mikesmitty/power-manifold/docs/src/content/docs/index.mdx

---
title: Power Manifold
description: A six-port USB-C power supply for single-board computers and other USB-C devices, with per-port control, priority-based power sharing and Home Assistant support.
template: splash
hero:
  image:
    # A plain img: Starlight would crop an image file to a square.
    html: 'Power Manifold chassis from the front right, showing the Ethernet jack, six numbered USB-C ports, the exhaust fan and the XT60 power input.'
  tagline: Six USB-C ports up to 100 W each, from one 24 V supply. Switch, name, limit and monitor every port from a browser or Home Assistant.
  actions:
    - text: Get started
      link: /setup/first-time-setup/
      icon: right-arrow
    - text: Source on GitHub
      link: https://github.com/mikesmitty/power-manifold
      icon: external
      variant: minimal
---

import { CardGrid, LinkCard } from '@astrojs/starlight/components';
import AdapterClutter from '../../components/AdapterClutter.astro';

<CardGrid>
	<LinkCard
		title="Set up your ports"
		description="Names, on/off at power-up, voltage and current limits, auto-off when charged."
		href="/guide/port-settings/"
	/>
	<LinkCard
		title="Share power between ports"
		description="Set the power budget and port priorities for a supply smaller than 600 W."
		href="/guide/sharing-power/"
	/>
	<LinkCard
		title="Add it to Home Assistant"
		description="Connect it to your MQTT broker and every port appears automatically."
		href="/guide/home-assistant/"
	/>
	<LinkCard
		title="Read the lights"
		description="What each port light and the chassis light mean, and what the button does."
		href="/guide/front-panel/"
	/>
	<LinkCard
		title="Troubleshooting"
		description="What a red light or a problem warning means, and what to do about it."
		href="/guide/troubleshooting/"
	/>
	<LinkCard
		title="Hardware and firmware"
		description="Architecture, building the firmware and the serial console, for developers."
		href="/developers/architecture/"
	/>
</CardGrid>

## What it does

<AdapterClutter />

<div class="features">
	<div class="feature">
		<h3>Six ports, up to 100 W each</h3>
		<p>Powers Raspberry Pis, phones, mini PCs and laptops at 5, 9, 12, 15 or 20 V, or PPS, with up to 5 A on a 5 A cable.</p>
	</div>
	<div class="feature">
		<h3>Shares power by priority</h3>
		<p>Set the size of your power supply and a priority for each port. When devices ask for more than the supply can give, the least important ports are turned down. Nothing is switched off.</p>
	</div>
	<div class="feature">
		<h3>Works with Home Assistant</h3>
		<p>Every port shows up with its power, an on/off switch and its settings, ready for dashboards, the energy panel and automations.</p>
	</div>
	<div class="feature">
		<h3>Status lights and live readings</h3>
		<p>A light above each port shows what it is doing, and the built-in web interface shows live power for every port.</p>
	</div>
</div>
