mikesmitty/power-manifold/docs/src/content/docs/integrations/ups.mdx

---
title: UPS power supply
description: Unofficial support for running Power Manifold from a Mean Well LAD-xxxBU battery-backed supply and seeing AC power and battery status in Home Assistant.
sidebar:
  order: 5
  badge:
    text: Unofficial
    variant: caution
---

import { Aside } from '@astrojs/starlight/components';
import Flow from '../../../components/Flow.astro';

<Aside type="caution" title="Unofficial">
UPS monitoring is not an officially supported configuration. The enclosure
provides no external access to the controller's UPS header, so connecting
the supply's serial lead requires opening the chassis. Support has been
verified only against a simulated supply.
</Aside>

Power Manifold can run from a Mean Well **LAD-xxxBU** security power supply,
which charges a battery and switches to it when AC power fails. Use a model
whose name ends in **BU**:

- **B** models charge a 24 V battery and have a 27.6 V output. The **A**
  models (13.8 V) and **C** models (about 41 V) don't suit Power
  Manifold's 24 V input.
- **U** models have the serial port Power Manifold needs.

## Connecting it

<Flow
	nodes={[
		{ title: 'AC power' },
		{ title: 'Mean Well LAD-xxxBU', detail: 'Runs from its battery when AC power fails' },
		{ title: 'Power Manifold', detail: 'Shows AC power and battery', highlight: true },
	]}
	links={[{ label: 'AC' }, { label: ['27.6 V to the XT60', 'CN2 to the UPS header'] }]}
/>

Connect the supply's output to the chassis XT60 input as usual. Then
connect the supply's serial port (on its CN2 header) to the controller
card's 3-pin **UPS** header. The controller finds the supply by itself
within a few seconds.

## What you get

Once the supply answers, the controller shows:

- whether AC power is on, whether it's running on battery and whether
  the battery is charging;
- battery voltage, AC voltage and load current.

These appear in the web interface's chassis line, in Home Assistant as *UPS AC
input*, *UPS on battery* and *UPS charging* plus three sensors, in the
[MQTT status](/integrations/mqtt/) and in the
[status JSON](/integrations/http-api/).

Running on battery, or a battery problem such as a missing, reversed or
failing battery, raises the **Problem** warning. You can use it to shut
down your Raspberry Pis gracefully before the battery runs out.

The UPS entities appear only once a supply answers. A chassis without one
shows none.
