mikesmitty/power-manifold/firmware/controller/src/engine/engine.c

#include "engine.h"
#include "i2c_diag.h"

#include <string.h>

#include "hardware/gpio.h"
#include "hardware/i2c.h"
#include "pico/flash.h"
#include "pico/stdlib.h"

#include "budget.h"
#include "fan_policy.h"
#include "flash_map.h"
#include "ipc.h"
#include "leds.h"
#include "manifold.h"
#include "pins.h"
#include "port_fsm.h"
#include "settings.h"
#include "stack_probe.h"
#include "tca9539.h"
#include "tca9548a.h"

#ifdef PWRMAN_FAKE_BLADES
#include "sim/sim_blades.h"
#include "sim/sim_inject.h"
#include "sim/sim_scenario.h"
#endif

#define TICK_MS 10 // 100 Hz supervisory rate
#define PRESENCE_REFRESH_TICKS 10 // full presence re-read every 100ms

static volatile bool alert_irq;
static volatile bool exp_irq;

// Expander reads missed in a row (one try per 100 ms) before the mux is
// reset, and before the expander itself is
#define EXP_FAILS_MUX_RESET 5
#define EXP_FAILS_RECOVER   50

static bool present[NUM_PORTS];
static uint8_t exp_fail_streak;
static bool warm_start;   // see engine_main
static uint8_t adopted;   // ports kept powered through the start

volatile uint8_t engine_stage;
volatile uint32_t engine_stage_us;
#define STAGE(n) do { engine_stage_us = time_us_32(); engine_stage = (n); } while (0)

// Delivered energy, integrated at the tick rate in mW·ms (µJ). uint64 is
// centuries of headroom; the mWh views in telemetry wrap after ~4.9 years
// of continuous 100W, which resets HA's total_increasing meters harmlessly.
static uint64_t port_energy_uj[NUM_PORTS];
static uint64_t total_energy_uj;

#ifndef PWRMAN_FAKE_BLADES
static void gpio_irq_handler(uint gpio, uint32_t events) {
    (void)events;
    if (gpio == PIN_ALERT_N) alert_irq = true;
    else if (gpio == PIN_EXP_INT_N) exp_irq = true;
}
#endif

// GLOBAL_ALERT# level; the sim stands in for the wire-OR line in fake builds
static bool alert_line_active(void) {
#ifdef PWRMAN_FAKE_BLADES
    return sim_alert_asserted();
#else
    return !gpio_get(PIN_ALERT_N);
#endif
}

static void refresh_presence(void) {
    uint16_t inputs;
    if (!tca9539_read_inputs(&inputs)) {
        // I2C trouble at the expander is chassis-level. After a few misses
        // the mux is reset, which frees a downstream segment that hung the
        // bus and costs no port anything. The expander keeps every EN where
        // it was through all of that, so it is left alone: only when it has
        // been out of reach for seconds — nobody can switch a port off then
        // — is it reset and its EN pattern written straight back
        // (tca9539_recover). That reset floats the EN lines for the moment
        // between the pulse and the write, which a running port will
        // notice; it is the last resort, not the first.
        exp_fail_streak++;
        if (exp_fail_streak % EXP_FAILS_MUX_RESET == 0) {
            tca9548a_hw_reset();
            if (exp_fail_streak == EXP_FAILS_MUX_RESET) {
                engine_evt_t e = {.type = EVT_PROBE_FAIL, .port = CHASSIS_EVT_PORT};
                ipc_evt_push(&e);
            }
        }
        if (exp_fail_streak >= EXP_FAILS_RECOVER) {
            exp_fail_streak = 0;
            tca9539_recover();
            engine_evt_t e = {.type = EVT_PROBE_FAIL, .port = CHASSIS_EVT_PORT, .code = 5};
            ipc_evt_push(&e);
        }
        return;
    }
    exp_fail_streak = 0;
    // A blade that reads as gone costs its port its power that tick, and
    // the read has nothing guarding it against a flipped bit. One that
    // says a seated blade has left is asked again, and only what both
    // reads agree on counts (PRES# is active low: a set bit is "absent").
    for (uint8_t i = 0; i < NUM_PORTS; i++) {
        if (!present[i] || tca9539_present_from(inputs, i)) continue;
        uint16_t again;
        if (!tca9539_read_inputs(&again)) return; // the next refresh decides
        inputs &= again;
        break;
    }
    for (uint8_t i = 0; i < NUM_PORTS; i++)
        present[i] = tca9539_present_from(inputs, i);
    // An expander back at its power-on registers (a reset nobody asked for)
    // has every EN floating: put its outputs and direction back and say so.
    if (tca9539_config_lost()) {
        tca9539_recover();
        engine_evt_t e = {.type = EVT_PROBE_FAIL, .port = CHASSIS_EVT_PORT, .code = 5};
        ipc_evt_push(&e);
    }
}

static void dispatch_cmd(const engine_cmd_t *cmd, uint32_t now_ms) {
    switch ((cmd_op_t)cmd->op) {
    case CMD_SET_BUDGET:
        budget_set_total(cmd->arg);
        break;
    case CMD_SET_CEILING:
        port_fsm_set_ceiling(cmd->arg);
        break;
    case CMD_FAN:
        fan_policy_set_manual(cmd->arg != 0);
        break;
    case CMD_FAN_AUTO:
        fan_policy_set_auto();
        break;
    case CMD_LED_BRIGHTNESS:
        leds_set_brightness((uint8_t)cmd->arg);
        break;
    case CMD_LED_IDENTIFY:
        leds_identify(now_ms + cmd->arg);
        break;
    case CMD_LED_CHASSIS:
        leds_set_chassis((uint8_t)cmd->arg);
        break;
    case CMD_LED_HOLD:
        leds_set_hold((uint8_t)cmd->arg);
        break;
    case CMD_LED_ACK:
        leds_ack(now_ms + cmd->arg);
        break;
    case CMD_I2C_DIAG:
#ifndef PWRMAN_FAKE_BLADES
        i2c_diag_run(cmd->arg);
#endif
        break;
    case CMD_SIM:
#ifdef PWRMAN_FAKE_BLADES
        if (sim_inject_op(cmd->arg) == SIM_SCENARIO) sim_scenario_set_running(sim_inject_value(cmd->arg) != 0);
        else sim_inject(cmd->port, cmd->arg);
#endif
        break;
    default:
        if (cmd->port < NUM_PORTS) port_fsm_cmd(cmd->port, cmd);
        break;
    }
}

void engine_main(void) {
    stack_probe_paint();
    STAGE(ENGINE_STAGE_ENTERED);
    // allow core 0 to write flash (settings) while this core is parked
    flash_safe_execute_core_init();

#ifndef PWRMAN_FAKE_BLADES
    i2c_init(I2C_BUS, I2C_BAUD);
    gpio_set_function(PIN_I2C_SDA, GPIO_FUNC_I2C);
    gpio_set_function(PIN_I2C_SCL, GPIO_FUNC_I2C);
    gpio_init(PIN_ALERT_N);
    gpio_set_dir(PIN_ALERT_N, GPIO_IN);
    // SDA/SCL and ALERT# have 4.7k external pull-ups on the controller card
    // (or wired on the pcie-breakout for a Pico 2 W). Every RP2350 pad boots
    // with its pull-down enabled and gpio_set_function/gpio_init leave it so;
    // that pull-down would sit across the external pull-up, eating noise
    // margin on every high level. Clear it.
#ifdef PWRMAN_INTERNAL_PULLUPS
    // Bench build without the three resistors: the pad pull-ups carry the
    // upstream bus (mux control, expander) at the 100 kHz in pins.h. Once a
    // mux channel is open that segment's 4.7k-to-5V pull-ups pass through
    // the switch and stiffen the upstream side as well.
    gpio_pull_up(PIN_I2C_SDA);
    gpio_pull_up(PIN_I2C_SCL);
    gpio_pull_up(PIN_ALERT_N);
#else
    gpio_disable_pulls(PIN_I2C_SDA);
    gpio_disable_pulls(PIN_I2C_SCL);
    gpio_disable_pulls(PIN_ALERT_N);
#endif
    // EXP_INT# is open-drain from the TCA9539 with no pull-up anywhere else;
    // without this the pad default (pull-down) reads it as permanently asserted.
    gpio_init(PIN_EXP_INT_N);
    gpio_set_dir(PIN_EXP_INT_N, GPIO_IN);
    gpio_pull_up(PIN_EXP_INT_N);
#else
    sim_reset();
#endif
    STAGE(ENGINE_STAGE_BUS_INIT);

    tca9548a_init();
    // A reboot with the backplane's 5 V up (firmware update, watchdog, a
    // console reboot) leaves the expander programmed and every EN where it
    // was — the reset lines are never asserted by a controller reset. Adopt
    // that state (warm start) rather than resetting it, so a reboot never
    // cuts port power; port_fsm_boot_inventory then takes the powered blades
    // under supervision without touching EN. Only an expander holding its
    // power-on state (cold start) is reset and configured from scratch,
    // outputs low FIRST, then direction (spec §6.4). While the controller
    // was down nothing arbitrated the budget or reacted to faults beyond
    // the blades' own limits; warm_probe reads what latched meanwhile.
    //
    // Which of the two it is rests on one register read, and reading it
    // wrong as cold takes every port down. So an expander that does not
    // answer is asked again for half a second, with the mux reset in between
    // (a downstream segment holding the bus is the likely cause), before
    // its silence is taken for a cold start; one that answers with anything
    // but our configuration is a cold start at once.
    tca9539_found_t found = tca9539_find();
    for (int tries = 0; found == TCA9539_NO_ANSWER && tries < 50; tries++) {
        tca9548a_hw_reset();
        sleep_ms(10);
        found = tca9539_find();
    }
    warm_start = found == TCA9539_OURS;
    if (!warm_start) tca9539_init();
    STAGE(ENGINE_STAGE_MUX_EXP);
    leds_init();
    leds_set_brightness(g_settings.led_brightness);
    leds_set_boot_style(g_settings.led_boot);
    leds_boot_sweep(to_ms_since_boot(get_absolute_time())); // also a chain-order check
    STAGE(ENGINE_STAGE_LEDS);

    budget_init(g_settings.budget_mw);
    port_fsm_init();
    fan_policy_init(g_settings.fan_auto != 0, (tca9539_outputs() >> TCA9539_FAN_BIT) & 1u);
    STAGE(ENGINE_STAGE_FSM);

#ifndef PWRMAN_FAKE_BLADES
    gpio_set_irq_enabled_with_callback(PIN_ALERT_N, GPIO_IRQ_EDGE_FALL, true,
                                       gpio_irq_handler);
    gpio_set_irq_enabled(PIN_EXP_INT_N, GPIO_IRQ_EDGE_FALL, true);
#endif
    STAGE(ENGINE_STAGE_IRQS);

#ifdef PWRMAN_FAKE_BLADES
    sim_scenario_tick(to_ms_since_boot(get_absolute_time())); // seat the demo blades first
#endif
    refresh_presence();
    // blades found powered stay so; the rest come up one at a time, in
    // priority order
    uint8_t powered = warm_start ? (uint8_t)(tca9539_outputs() & 0x3F) : 0; // EN1..EN6 = P00..P05
    adopted = port_fsm_boot_inventory(present, powered, to_ms_since_boot(get_absolute_time()));
    STAGE(ENGINE_STAGE_PRESENCE);

    uint32_t tick = 0;
    absolute_time_t next = get_absolute_time();
    for (;;) {
        next = delayed_by_ms(next, TICK_MS);
        uint32_t now_ms = to_ms_since_boot(get_absolute_time());

#ifdef PWRMAN_FAKE_BLADES
        sim_scenario_tick(now_ms);
#endif

        engine_cmd_t cmd;
        while (ipc_cmd_pop(&cmd)) dispatch_cmd(&cmd, now_ms);

        // a controller image still on trial leaves the blades' firmware alone
        port_fsm_hold_updates(flash_map_update_pending());

        // Fault line first: it is wire-OR'd, so sweep all powered ports.
        // Level-check as well as the IRQ flag in case an edge was missed.
        if (alert_irq || alert_line_active()) {
            alert_irq = false;
            port_fsm_alert_sweep(now_ms);
        }

        if (exp_irq || (tick % PRESENCE_REFRESH_TICKS) == 0) {
            exp_irq = false;
            refresh_presence();
        }

        telemetry_t t;
        memset(&t, 0, sizeof(t));
        for (uint8_t i = 0; i < NUM_PORTS; i++)
            port_fsm_tick(i, present[i], now_ms, &t.port[i]);

        for (uint8_t i = 0; i < NUM_PORTS; i++) {
            t.total_mw += t.port[i].power_mw;
            port_energy_uj[i] += (uint64_t)t.port[i].power_mw * TICK_MS;
            t.port[i].energy_mwh = (uint32_t)(port_energy_uj[i] / 3600000u);
        }
        total_energy_uj += (uint64_t)t.total_mw * TICK_MS;
        t.energy_mwh = (uint32_t)(total_energy_uj / 3600000u);
        t.reserved_mw = budget_reserved();
        t.budget_mw = budget_total();

        fan_policy_tick(&t, now_ms);
        t.fan_on = fan_policy_on();
        t.fan_auto = fan_policy_auto();
        t.alert_active = alert_line_active();
        t.warm_start = warm_start;
        t.adopted = adopted;

        ipc_snapshot_publish(&t);
        leds_render(&t, now_ms);
        ipc_engine_heartbeat();
        STAGE(ENGINE_STAGE_LOOP);

        tick++;
        sleep_until(next);
    }
}
