mikesmitty/power-manifold/firmware/controller/src/settings.h

#pragma once

#include <stdbool.h>
#include <stdint.h>

#include "manifold.h"

// Persistent configuration. Stored as a ping-pong pair of 4KB sectors: saves
// alternate sectors with an incrementing sequence number, so a power failure
// mid-write leaves the previous copy intact. The pair lives at the start of
// the partition table's "data" partition (see flash_map.h), falling back to
// the legacy last-two-sectors-of-flash location on unpartitioned boards.
//
// The record is the struct below as it sits in memory, crc last. A new
// layout version only ever appends fields (settings.c pins every shipped
// offset), so a record of any later version begins with a complete copy of
// this one, and payload_len tells a firmware that meets a version it does
// not know where that record's crc sits — see settings.c.

#define SETTINGS_MAGIC 0x504D4643u // "PMFC"
#define PORT_NAME_MAX  23          // bytes, excluding the NUL
#define MQTT_CA_MAX    2048        // bytes of DER: room for any public root, with a margin
#define HOSTNAMES_MAX  128         // bytes of the hostnames list, with the NUL
#define UPDATE_VERSION_MAX 16     // x.y.z with the NUL, as update_latest.h
// settings mqtt_tls, the broker link's transport (net/mqtt_tls.h)
#define MQTT_TLS_OFF        0 // plain MQTT
#define MQTT_TLS_VERIFIED   1 // TLS; the broker's chain must lead to mqtt_ca, or to a built-in Let's Encrypt root when none is installed
#define MQTT_TLS_UNVERIFIED 2 // TLS that checks nothing

typedef struct {
    uint32_t magic;
    uint32_t version;  // struct layout version
    uint32_t seq;      // ping-pong sequence
    char     wifi_ssid[33];
    char     wifi_pass[65];
    char     mqtt_host[64]; // empty = MQTT disabled
    uint16_t mqtt_port;
    char     mqtt_user[33];
    char     mqtt_pass[65];
    char     device_name[32]; // hostname / mDNS / MQTT topic id
    char     api_token[33];   // empty = REST mutations unauthenticated
    uint32_t budget_mw;       // chassis power budget
    uint32_t port_limit_ma[NUM_PORTS]; // per-port PDO current ceiling
    uint8_t  port_priority[NUM_PORTS]; // 0 = highest; throttle victims picked from the bottom
    uint8_t  led_brightness;  // 0-255
    // -- added in layout version 2 (older records upgrade on load) --
    uint8_t  fan_auto;        // 1: engine drives the fan from total power
    uint16_t fan_on_w;        // auto: on at/above this
    uint16_t fan_off_w;       // auto: off at/below this (hysteresis band)
    // -- added in layout version 3 --
    uint16_t fan_on_ma;       // auto: also on while any contract exceeds this (0 = off)
    // -- added in layout version 4 --
    uint8_t  led_boot;        // LED_BOOT_*: power-up sweep style
    // -- added in layout version 5 --
    char     port_name[NUM_PORTS][PORT_NAME_MAX + 1]; // "" = "Port N"
    // -- added in layout version 6 --
    uint8_t  port_boot[NUM_PORTS]; // PORT_BOOT_*: administrative state at power-up
    uint8_t  port_off_mask;        // bit N set: port N was last switched off (PORT_BOOT_LAST)
    // -- added in layout version 7 --
    uint8_t  ip_static;   // 0: DHCP (default); 1: the static address below (see net.h)
    uint32_t ip_addr;     // IPv4 in network byte order (ip4_addr_t.addr)
    uint32_t ip_mask;
    uint32_t ip_gw;
    uint32_t ip_dns;      // 0: DHCP's servers (static mode: the gateway); else always used
    // -- added in layout version 8 --
    char     syslog_host[64]; // "" = no remote log sink (see log_sink.h)
    uint16_t syslog_port;     // UDP, default 514
    // -- added in layout version 9 --
    uint16_t charged_mw;      // charge-complete: draw under this (0 = detection off)...
    uint8_t  charged_min;     // ...for this many minutes marks the sink charged
    uint8_t  port_auto_off;   // bit N set: port N switches off once charged
    uint16_t port_sleep_min[NUM_PORTS]; // switch off this long after a sink attaches (0 = never)
    // -- added in layout version 10 --
    uint8_t  led_dim;          // brightness while dimmed (night window / idle), see led_sched.h
    uint16_t led_night_start;  // minutes after local midnight; start == end = no window
    uint16_t led_night_end;
    uint16_t led_idle_min;     // dim after this long without a port event (0 = never)
    int16_t  tz_offset_min;    // local time = UTC + this (SNTP is UTC; no tz database)
    // -- added in layout version 11 --
    uint16_t port_max_mv[NUM_PORTS]; // voltage cap: highest PDO advertised (PORT_VOLT_MAX_MV = all)
    // -- added in layout version 12 --
    uint16_t vin_cal;         // bus-voltage gain trim, permille (see vin.h)
    // -- added in layout version 13 --
    uint8_t  retired_13;           // a setting since removed (blades always take the bundled firmware); kept so that later fields do not move
    uint8_t  blade_boot_via_loader; // 1: gen-3 blades are set to boot through their ROM bootloader, once idle (blade_regs.h BLADE_BOOT_VIA_LOADER)
    uint8_t  blade_watch_s;        // a gen-3 blade with EN low resets into its bootloader after this long without the controller (0 = never)
    // -- added in layout version 14 --
    uint16_t payload_len;     // bytes the crc covers (= its offset): lets an older firmware read this record
    // -- added in layout version 15 --
    char     update_url[64];  // where to ask for the newest release, "" = never ask (update_latest.h)
    // -- added in layout version 16 --
    char     ntp_server[64];  // time server; "" = the one DHCP names, else NET_NTP_DEFAULT (net.h)
    // -- added in layout version 17 --
    uint8_t  mqtt_tls;        // MQTT_TLS_OFF, _VERIFIED or _UNVERIFIED (above; net/mqtt_tls.h)
    uint16_t mqtt_ca_len;     // bytes of mqtt_ca in use, 0 = none installed
    uint8_t  mqtt_ca[MQTT_CA_MAX]; // one DER certificate: the broker's CA, or the broker's own self-signed one
    // -- added in layout version 18 --
    uint8_t  retired_18;      // a per-port setting since removed; kept so that later fields do not move
    // -- added in layout version 19 --
    char     hostnames[HOSTNAMES_MAX]; // extra names the web server answers to, space-separated, lowercase (net/http_req.h)
    // -- added in layout version 20 --
    uint32_t update_postpone;  // unix time automatic installs are put off until, 0 = not put off (update_auto.h)
    uint32_t update_seen_at;   // unix time update_seen became known, 0 = the clock was not set
    uint8_t  update_auto;      // 1: newer releases install by themselves
    uint8_t  update_wait_days; // days update_seen waits before it installs
    char     update_seen[UPDATE_VERSION_MAX]; // the newer release the wait is counted for
    char     update_skip[UPDATE_VERSION_MAX]; // never installed automatically: skipped, or rolled back
    char     update_tried[UPDATE_VERSION_MAX]; // the image a restart went into; checked at the next boot
    // -- added in layout version 21 --
    uint8_t  https;            // 1: the web server listens on 443 and port 80 only redirects (net/https.h)
    uint32_t crc; // must remain last
} settings_t;

extern settings_t g_settings;

void settings_load(void);     // falls back to defaults on empty/corrupt flash
bool settings_save(void);     // core 0 only; engine pauses briefly via flash_safe_execute
void settings_defaults(void);
// Factory reset of the store: erases every stored copy, the previous slot
// and any legacy record included, then saves defaults as the only record.
// Core 0 only, like settings_save. False if any erase or the save failed.
bool settings_wipe(void);

// Per-port label for the UI and Home Assistant: the stored name, or "Port N"
// when none is set (port is 0-based).
const char *settings_port_name(unsigned port);
// A label is at most PORT_NAME_MAX bytes of printable text (no control
// characters, no leading or trailing spaces); empty clears it.
bool settings_port_name_valid(const char *s);

// Bookkeeping for the PORT_BOOT_LAST policy: every surface that switches a
// port on or off records the new state here (core 0). Returns true when the
// change is worth a flash write — the port's policy is "last" and the state
// actually moved — so the caller can settings_save_later().
bool settings_port_admin_note(unsigned port, bool on);
// PORT_BOOT_* <-> "on" / "off" / "last"
const char *settings_port_boot_name(uint8_t policy);
bool settings_port_boot_parse(const char *s, uint8_t *policy);
// Voltage cap: one of the fixed PDO voltages, 5000/9000/12000/15000/20000 mV
bool settings_port_volt_valid(unsigned mv);
// "9", "9V" or "9 V" (volts) -> mV; false unless it names a valid cap
bool settings_port_volt_parse(const char *s, uint16_t *mv);

// Debounced persistence for remote mutations (MQTT/REST): mark now, and the
// main loop's settings_save_poll flushes once things go quiet for a few
// seconds. Returns 0 when idle, 1 after a successful save, -1 on failure.
void settings_save_later(void);
int  settings_save_poll(uint32_t now_ms);
bool settings_save_pending(void); // a settings_save_later not yet flushed

// One-shot re-home of settings found at the legacy location on a freshly
// partitioned board. Needs flash writes, so call from core 0 once the engine
// is running (flash_safe_execute refuses before core 1 can be parked).
bool settings_migration_pending(void);
bool settings_migrate(void);
