mikesmitty/power-manifold/firmware/controller/src/settings_json.c

#include "settings_json.h"

#include <stdarg.h>
#include <stdio.h>
#include <string.h>

#include "ip4_text.h"
#include "led_sched.h"
#include "net/http_req.h"
#include "net/jsonlite.h"
#include "net/mqtt_tls.h"
#include "pem.h"
#include "manifold.h"
#include "vin.h"
#include "update_latest.h"

#define STR_(x) #x
#define STR(x) STR_(x)

// ---- building ---------------------------------------------------------------

static size_t putf(char *out, size_t cap, size_t off, const char *fmt, ...) {
    if (off >= cap) return cap;
    va_list ap;
    va_start(ap, fmt);
    int n = vsnprintf(out + off, cap - off, fmt, ap);
    va_end(ap);
    if (n < 0) return cap;
    return off + (size_t)n >= cap ? cap : off + (size_t)n;
}

// "key":"escaped value",
static size_t put_str(char *out, size_t cap, size_t off, const char *key, const char *val) {
    off = putf(out, cap, off, "\"%s\":\"", key);
    if (off < cap) off += json_escape(out + off, cap - off, val);
    return putf(out, cap, off, "\",");
}

static size_t put_ip(char *out, size_t cap, size_t off, const char *key, uint32_t addr) {
    char t[16];
    ip4_format(t, sizeof(t), addr);
    return put_str(out, cap, off, key, t);
}

size_t settings_json_build(char *out, size_t cap, const settings_t *s,
                           const settings_json_opts_t *o) {
    if (!cap) return 0;
    size_t off = putf(out, cap, 0, "{");
    off = put_str(out, cap, off, "name", s->device_name);
    off = put_str(out, cap, off, "wifi_ssid", s->wifi_ssid);
    off = put_str(out, cap, off, "mqtt_host", s->mqtt_host);
    off = putf(out, cap, off, "\"mqtt_port\":%u,", s->mqtt_port);
    off = put_str(out, cap, off, "mqtt_user", s->mqtt_user);
    off = putf(out, cap, off, "\"mqtt_pass_set\":%s,\"token_set\":%s,\"setup\":%s,",
               s->mqtt_pass[0] ? "true" : "false", s->api_token[0] ? "true" : "false",
               o->setup ? "true" : "false");
    off = putf(out, cap, off, "\"budget_w\":%lu,\"fan_mode\":\"%s\",\"fan_on_w\":%u,"
               "\"fan_off_w\":%u,\"fan_on_ma\":%u,\"led_brightness\":%u,\"led_boot\":\"%s\",",
               (unsigned long)(s->budget_mw / 1000u),
               s->fan_auto ? "auto" : (o->fan_on ? "on" : "off"),
               s->fan_on_w, s->fan_off_w, s->fan_on_ma, s->led_brightness,
               s->led_boot == LED_BOOT_RAINBOW ? "rainbow" : "white");
    char night[16];
    night_format(night, sizeof(night), s->led_night_start, s->led_night_end);
    off = putf(out, cap, off, "\"led_dim\":%u,\"led_night\":\"%s\",\"led_idle_min\":%u,"
               "\"tz_offset_min\":%d,", s->led_dim, night, s->led_idle_min, s->tz_offset_min);
    off = putf(out, cap, off, "\"ip_mode\":\"%s\",", s->ip_static ? "static" : "dhcp");
    off = put_ip(out, cap, off, "ip", s->ip_addr);
    off = put_ip(out, cap, off, "netmask", s->ip_mask);
    off = put_ip(out, cap, off, "gateway", s->ip_gw);
    off = put_ip(out, cap, off, "dns", s->ip_dns);
    off = put_str(out, cap, off, "syslog_host", s->syslog_host);
    off = put_str(out, cap, off, "update_url", s->update_url);
    off = putf(out, cap, off, "\"update_auto\":%s,", s->update_auto ? "true" : "false");
    off = put_str(out, cap, off, "ntp_server", s->ntp_server);
    off = put_str(out, cap, off, "hostnames", s->hostnames);
    // the certificate goes out as PEM, its line ends already escaped
    off = putf(out, cap, off, "\"mqtt_tls\":%s,\"mqtt_tls_verify\":%s,\"mqtt_ca\":\"",
               s->mqtt_tls != MQTT_TLS_OFF ? "true" : "false", s->mqtt_tls != MQTT_TLS_UNVERIFIED ? "true" : "false");
    if (off < cap && s->mqtt_ca_len) {
        size_t n = der_to_pem(s->mqtt_ca, s->mqtt_ca_len, out + off, cap - off, "\\n");
        off = n ? off + n : cap; // 0 = it did not fit: the check at the end reports that
    }
    off = putf(out, cap, off, "\",");
    off = putf(out, cap, off, "\"syslog_port\":%u,\"charged_mw\":%u,\"charged_min\":%u,",
               s->syslog_port, s->charged_mw, s->charged_min);
    // the bus-voltage trim belongs to this unit's divider: shown, never backed up
    if (!o->export) off = putf(out, cap, off, "\"vin_cal\":%u,", s->vin_cal);
    // HTTPS needs the certificate installed on this unit, which no export
    // carries: shown, never backed up, so an import cannot turn it on
    if (!o->export) off = putf(out, cap, off, "\"https\":%s,", s->https ? "true" : "false");
    off = putf(out, cap, off, "\"blade_boot_via_loader\":%s,\"blade_watch_s\":%u,\"port_names\":[",
               s->blade_boot_via_loader ? "true" : "false", s->blade_watch_s);
    for (int i = 0; i < NUM_PORTS; i++) {
        off = putf(out, cap, off, "%s\"", i ? "," : "");
        if (off < cap) off += json_escape(out + off, cap - off, s->port_name[i]);
        off = putf(out, cap, off, "\"");
    }
    off = putf(out, cap, off, "],\"port_limits_ma\":[");
    for (int i = 0; i < NUM_PORTS; i++)
        off = putf(out, cap, off, "%s%lu", i ? "," : "", (unsigned long)s->port_limit_ma[i]);
    off = putf(out, cap, off, "],\"port_max_v\":[");
    for (int i = 0; i < NUM_PORTS; i++)
        off = putf(out, cap, off, "%s%u", i ? "," : "", s->port_max_mv[i] / 1000);
    off = putf(out, cap, off, "],\"port_boot\":[");
    for (int i = 0; i < NUM_PORTS; i++)
        off = putf(out, cap, off, "%s\"%s\"", i ? "," : "", settings_port_boot_name(s->port_boot[i]));
    off = putf(out, cap, off, "],\"port_priorities\":[");
    for (int i = 0; i < NUM_PORTS; i++)
        off = putf(out, cap, off, "%s%u", i ? "," : "", s->port_priority[i]);
    off = putf(out, cap, off, "],\"port_auto_off\":[");
    for (int i = 0; i < NUM_PORTS; i++)
        off = putf(out, cap, off, "%s%u", i ? "," : "", (s->port_auto_off >> i) & 1);
    off = putf(out, cap, off, "],\"port_sleep_min\":[");
    for (int i = 0; i < NUM_PORTS; i++)
        off = putf(out, cap, off, "%s%u", i ? "," : "", s->port_sleep_min[i]);
    off = putf(out, cap, off, "]");
    if (o->secrets) {
        off = putf(out, cap, off, ",");
        off = put_str(out, cap, off, "wifi_pass", s->wifi_pass);
        off = put_str(out, cap, off, "mqtt_pass", s->mqtt_pass);
        off = put_str(out, cap, off, "token", s->api_token);
        off--; // the trailing comma
    }
    if (o->export) off = putf(out, cap, off, ",\"format\":1,\"fw\":\"%s\"", FW_VERSION);
    off = putf(out, cap, off, "}");
    if (off >= cap) { // truncated: never hand out a torn object
        out[0] = '\0';
        return 0;
    }
    return off;
}

// ---- applying ---------------------------------------------------------------

static bool header_safe(const char *s) { // printable ASCII, no spaces
    for (; *s; s++) {
        if ((unsigned char)*s < 0x21 || (unsigned char)*s > 0x7E) return false;
    }
    return true;
}

static bool no_controls(const char *s) {
    for (; *s; s++) {
        if ((unsigned char)*s < 0x20 || (unsigned char)*s == 0x7F) return false;
    }
    return true;
}

static bool valid_name(const char *s) { // one hostname label
    size_t n = strlen(s);
    if (!n || s[0] == '-' || s[n - 1] == '-') return false;
    for (; *s; s++) {
        if (!((*s >= 'a' && *s <= 'z') || (*s >= 'A' && *s <= 'Z') || (*s >= '0' && *s <= '9') ||
              *s == '-'))
            return false;
    }
    return true;
}

// string field with a length check and a validator; NULL when fine
static const char *take_str(const char *body, const char *key, char *dst, size_t cap,
                            bool (*ok)(const char *), const char *too_long, const char *bad) {
    int r = json_get_str(body, key, dst, cap);
    if (r < 0) return too_long;
    if (r > 0 && ok && !ok(dst)) return bad;
    return NULL;
}

const char *settings_json_apply(const char *body, settings_t *s, bool via_setup,
                                settings_apply_t *out) {
    memset(out, 0, sizeof(*out));
    const char *err;
    long v;

    if ((err = take_str(body, "name", s->device_name, sizeof(s->device_name), valid_name,
                        "name too long", "name: letters, digits and hyphens only")))
        return err;
    if ((err = take_str(body, "wifi_ssid", s->wifi_ssid, sizeof(s->wifi_ssid), no_controls,
                        "wifi_ssid too long", "wifi_ssid: no control characters")))
        return err;
    if ((err = take_str(body, "wifi_pass", s->wifi_pass, sizeof(s->wifi_pass), no_controls,
                        "wifi_pass too long", "wifi_pass: no control characters")))
        return err;
    if ((err = take_str(body, "mqtt_host", s->mqtt_host, sizeof(s->mqtt_host), header_safe,
                        "mqtt_host too long", "mqtt_host: no spaces or control characters")))
        return err;
    if ((err = take_str(body, "mqtt_user", s->mqtt_user, sizeof(s->mqtt_user), no_controls,
                        "mqtt_user too long", "mqtt_user: no control characters")))
        return err;
    if ((err = take_str(body, "mqtt_pass", s->mqtt_pass, sizeof(s->mqtt_pass), no_controls,
                        "mqtt_pass too long", "mqtt_pass: no control characters")))
        return err;
    if ((err = take_str(body, "token", s->api_token, sizeof(s->api_token), header_safe,
                        "token too long", "token: no spaces or control characters")))
        return err;
    if ((err = take_str(body, "syslog_host", s->syslog_host, sizeof(s->syslog_host), header_safe,
                        "syslog_host too long", "syslog_host: no spaces or control characters")))
        return err;
    if ((err = take_str(body, "ntp_server", s->ntp_server, sizeof(s->ntp_server), header_safe,
                        "ntp_server too long", "ntp_server: no spaces or control characters")))
        return err;
    // The certificate arrives as PEM text (or bare base64) and is stored as
    // DER; empty removes it. The text buffer is static because the HTTP
    // server runs this on the IRQ stack.
    static char ca_text[4096];
    int got_ca = json_get_str(body, "mqtt_ca", ca_text, sizeof(ca_text));
    if (got_ca < 0) return "mqtt_ca too long";
    if (got_ca > 0) {
        if (!ca_text[0]) {
            s->mqtt_ca_len = 0;
            memset(s->mqtt_ca, 0, sizeof(s->mqtt_ca));
        } else {
            size_t n = pem_to_der(ca_text, s->mqtt_ca, sizeof(s->mqtt_ca));
            if (!n) return "mqtt_ca: PEM or base64 of one certificate, up to " STR(MQTT_CA_MAX) " bytes of DER, or empty";
            if (!der_cert_shape_ok(s->mqtt_ca, n)) return "mqtt_ca: not a DER certificate";
            if ((err = mqtt_ca_check(s->mqtt_ca, n))) return err;
            memset(s->mqtt_ca + n, 0, sizeof(s->mqtt_ca) - n);
            s->mqtt_ca_len = (uint16_t)n;
        }
    }
    char names[2 * HOSTNAMES_MAX];
    int got_names = json_get_str(body, "hostnames", names, sizeof(names));
    if (got_names) {
        if (got_names < 0) return "hostnames: the list is too long";
        if ((err = http_req_hostnames_parse(names, s->hostnames, sizeof(s->hostnames)))) return err;
    }
    char source[sizeof(s->update_url) + 8];
    int got = json_get_str(body, "update_url", source, sizeof(source));
    if (got) {
        if (got < 0 || !update_source_valid(source, sizeof(s->update_url)))
            return "update_url: http://host[:port][/path] without a trailing slash, or empty";
        strcpy(s->update_url, source);
    }
    if (json_get_int(body, "mqtt_port", &v)) {
        if (v < 1 || v > 65535) return "mqtt_port out of range";
        s->mqtt_port = (uint16_t)v;
    }
    if (json_get_int(body, "syslog_port", &v)) {
        if (v < 1 || v > 65535) return "syslog_port out of range";
        s->syslog_port = (uint16_t)v;
    }
    if (json_get_int(body, "charged_mw", &v)) {
        if (v < 0 || v > 20000) return "charged_mw: 0-20000 (0 disables)";
        s->charged_mw = (uint16_t)v;
    }
    if (json_get_int(body, "charged_min", &v)) {
        if (v < 1 || v > 255) return "charged_min: 1-255";
        s->charged_min = (uint8_t)v;
    }
    // vin_cal is left as it is: the bus-sag cap acts on the trimmed
    // reading, so the trim is set only from the serial console, against a
    // meter. Exports leave it out, and a file that names it changes nothing.
    bool b;
    // Two booleans spell the three link states. A file that names only one
    // keeps the other half of the state; mqtt_tls_verify is true unless the
    // file says otherwise and is moot while TLS is off.
    bool tls, verify;
    bool got_tls = json_get_bool(body, "mqtt_tls", &tls);
    bool got_verify = json_get_bool(body, "mqtt_tls_verify", &verify);
    if (got_tls || got_verify) {
        if (!got_tls) tls = s->mqtt_tls != MQTT_TLS_OFF;
        if (!got_verify) verify = s->mqtt_tls != MQTT_TLS_UNVERIFIED;
        s->mqtt_tls = !tls ? MQTT_TLS_OFF : verify ? MQTT_TLS_VERIFIED : MQTT_TLS_UNVERIFIED;
    }
    if (json_get_bool(body, "update_auto", &b)) s->update_auto = b;
    // whether a certificate is installed is the HTTP server's check
    if (json_get_bool(body, "https", &b)) s->https = b;
    if (json_get_bool(body, "blade_boot_via_loader", &b)) s->blade_boot_via_loader = b;
    if (json_get_int(body, "blade_watch_s", &v)) {
        if (v < 0 || v > 255) return "blade_watch_s: 0-255 (0 disables)";
        s->blade_watch_s = (uint8_t)v;
    }
    if (via_setup && !s->api_token[0]) return "set an API token to finish setup";

    // operational fields
    if (json_get_int(body, "budget_w", &v)) {
        if (v < BUDGET_MIN_W || v > BUDGET_MAX_W) return "budget_w out of range";
        s->budget_mw = (uint32_t)v * 1000u;
    }
    if (json_get_int(body, "fan_on_w", &v)) {
        if (v < 1 || v > 1000) return "fan_on_w: 1-1000";
        s->fan_on_w = (uint16_t)v;
        out->fan_thresholds = true;
    }
    if (json_get_int(body, "fan_off_w", &v)) {
        if (v < 0 || v > 1000) return "fan_off_w: 0-1000";
        s->fan_off_w = (uint16_t)v;
        out->fan_thresholds = true;
    }
    if (json_get_int(body, "fan_on_ma", &v)) {
        if (v < 0 || v > 10000) return "fan_on_ma: 0-10000 (0 disables)";
        s->fan_on_ma = (uint16_t)v;
        out->fan_thresholds = true;
    }
    char mode[8];
    int m = json_get_str(body, "fan_mode", mode, sizeof(mode));
    if (m != 0) {
        if (m > 0 && !strcmp(mode, "auto")) {
            s->fan_auto = 1;
        } else if (m > 0 && (!strcmp(mode, "on") || !strcmp(mode, "off"))) {
            s->fan_auto = 0;
            out->fan_manual_on = mode[1] == 'n';
        } else {
            return "fan_mode: auto, on or off";
        }
        out->fan_mode_given = true;
    }
    if ((out->fan_thresholds || m != 0) && s->fan_off_w >= s->fan_on_w)
        return "fan_off_w must be below fan_on_w";
    if (json_get_int(body, "led_brightness", &v)) {
        if (v < 0 || v > 255) return "led_brightness: 0-255";
        s->led_brightness = (uint8_t)v;
    }
    char t[20];
    int r = json_get_str(body, "led_boot", t, sizeof(t));
    if (r != 0) {
        if (r > 0 && !strcmp(t, "white")) s->led_boot = LED_BOOT_WHITE;
        else if (r > 0 && !strcmp(t, "rainbow")) s->led_boot = LED_BOOT_RAINBOW;
        else return "led_boot: white or rainbow";
    }
    if (json_get_int(body, "led_dim", &v)) {
        if (v < 0 || v > 255) return "led_dim: 0-255";
        s->led_dim = (uint8_t)v;
    }
    r = json_get_str(body, "led_night", t, sizeof(t));
    if (r < 0 || (r > 0 && !night_parse(t, &s->led_night_start, &s->led_night_end)))
        return "led_night: HH:MM-HH:MM or empty";
    if (json_get_int(body, "led_idle_min", &v)) {
        if (v < 0 || v > 1440) return "led_idle_min: 0-1440";
        s->led_idle_min = (uint16_t)v;
    }
    if (json_get_int(body, "tz_offset_min", &v)) {
        if (v < -720 || v > 840) return "tz_offset_min: -720 to 840";
        s->tz_offset_min = (int16_t)v;
    }

    // addressing: any subset, validated as a whole
    r = json_get_str(body, "ip_mode", t, sizeof(t));
    if (r != 0) {
        if (r > 0 && !strcmp(t, "dhcp")) s->ip_static = 0;
        else if (r > 0 && !strcmp(t, "static")) s->ip_static = 1;
        else return "ip_mode: dhcp or static";
    }
    static const struct { const char *key; size_t off; } IPF[] = {
        {"ip", offsetof(settings_t, ip_addr)}, {"netmask", offsetof(settings_t, ip_mask)},
        {"gateway", offsetof(settings_t, ip_gw)}, {"dns", offsetof(settings_t, ip_dns)},
    };
    for (size_t i = 0; i < sizeof(IPF) / sizeof(IPF[0]); i++) {
        r = json_get_str(body, IPF[i].key, t, sizeof(t));
        if (r == 0) continue;
        uint32_t a = 0;
        if (r < 0 || (t[0] && !ip4_parse(t, &a))) return "ip/netmask/gateway/dns: dotted quad or empty";
        memcpy((uint8_t *)s + IPF[i].off, &a, sizeof(a));
    }
    if (s->ip_static && (!s->ip_addr || !s->ip_gw || !ip4_mask_valid(s->ip_mask)))
        return "static addressing needs ip, a valid netmask and gateway";

    // per-port arrays
    for (int i = 0; i < NUM_PORTS; i++) {
        if (json_get_int_at(body, "port_limits_ma", (unsigned)i, &v)) {
            if (v < PORT_LIMIT_MIN_MA || v > PORT_LIMIT_MAX_MA)
                return "port_limits_ma: " STR(PORT_LIMIT_MIN_MA) "-" STR(PORT_LIMIT_MAX_MA) " mA each";
            s->port_limit_ma[i] = (uint32_t)v;
        }
        if (json_get_int_at(body, "port_max_v", (unsigned)i, &v)) {
            if (v < 0 || !settings_port_volt_valid((unsigned)v * 1000u)) return "port_max_v: 5, 9, 12, 15 or 20 each";
            s->port_max_mv[i] = (uint16_t)(v * 1000);
        }
        if (json_get_int_at(body, "port_priorities", (unsigned)i, &v)) {
            if (v < 0 || v > 255) return "port_priorities: 0-255 each";
            s->port_priority[i] = (uint8_t)v;
        }
        if (json_get_int_at(body, "port_auto_off", (unsigned)i, &v)) {
            if (v < 0 || v > 1) return "port_auto_off: 0 or 1 each";
            if (v) s->port_auto_off |= (uint8_t)(1u << i);
            else s->port_auto_off &= (uint8_t)~(1u << i);
        }
        if (json_get_int_at(body, "port_sleep_min", (unsigned)i, &v)) {
            if (v < 0 || v > PORT_SLEEP_MAX_MIN) return "port_sleep_min: 0-" STR(PORT_SLEEP_MAX_MIN) " each";
            s->port_sleep_min[i] = (uint16_t)v;
        }
        r = json_get_str_at(body, "port_names", (unsigned)i, s->port_name[i], sizeof(s->port_name[i]));
        if (r < 0) return "port_names: at most " STR(PORT_NAME_MAX) " characters each";
        if (r > 0 && !settings_port_name_valid(s->port_name[i]))
            return "port_names: printable text, no leading or trailing spaces";
        r = json_get_str_at(body, "port_boot", (unsigned)i, t, sizeof(t));
        if (r < 0 || (r > 0 && !settings_port_boot_parse(t, &s->port_boot[i])))
            return "port_boot: on, off or last each";
    }
    return NULL;
}
