mikesmitty/power-manifold/firmware/charger-module/src/supervisor.c

#include "supervisor.h"

#include <stdbool.h>
#include <stdint.h>

#include "blade.h"
#include "blade_regs.h"
#include "console.h"
#include "hw.h"
#include "meter.h"
#include "port.h"
#include "power.h"
#include "regmap.h"
#include "sense.h"
#include "stack.h"

#define SAMPLE_MS          10
#define REPORT_MS          1000
// A temperature reading past its limit has to hold for this many samples
// before it counts. Noise cannot keep it there, a glitch from the switching
// stage might, and a latched fault costs a trip to the controller to clear.
#define TEMP_TRIP_SAMPLES  5
// EN high to the first word on the private bus. The TPS55288 datasheet gives
// no figure; this is the allowance the controller makes for the gen-2 blade.
#define CONVERTER_WAKE_MS  50

static regmap_live_t live;
static regmap_config_t cfg;
static bool en, conv_pending, line_up;
static bool leaving; // the MCU is on its way to a reset (only ever seen off the board)
static uint32_t en_ms, sample_ms, report_ms;
static uint32_t seen_ms, seen_count; // the controller's last transaction
static uint8_t hot_conv, hot_plug;   // consecutive samples past the limit
static uint8_t warm_conv_n, warm_plug_n; // consecutive samples at or above the warning level
static bool    warm_conv, warm_plug;

static void raise(uint16_t faults) {
    hw_backplane_lock();
    regmap_raise(faults);
    hw_backplane_unlock();
}

static uint16_t faults_now(void) {
    hw_backplane_lock();
    uint16_t faults = regmap_faults();
    hw_backplane_unlock();
    return faults;
}

static uint16_t fault_of(power_result_t r) {
    switch (r) {
    case POWER_OK:      return 0;
    case POWER_TRIPPED: return BLADE_FAULT_OVP;
    case POWER_TIMEOUT: return BLADE_FAULT_VBUS;
    default:            return BLADE_FAULT_BUS;
    }
}

static void line_raise(void) {
    uint16_t f = fault_of(power_port_up());
    line_up = !f;
    if (f) {
        power_port_down();
        raise(f);
    }
}

static void follow_en(uint32_t now) {
    if (hw_en() != en) {
        en = !en;
        en_ms = now;
        conv_pending = en; // shutdown cost the converter its registers
        if (!en) power_converter_lost();
        console_str(en ? "EN high\n" : "EN low\n");
    }
    if (conv_pending && now - en_ms >= CONVERTER_WAKE_MS) {
        conv_pending = false;
        raise(fault_of(power_converter_up()));
    }
}

// The port goes dark before the MCU leaves: the ROM bootloader would not
// touch it, but the switch should not be found closed by whoever comes next.
static void leave_for_loader(bool program_boot_option) {
    console_str(program_boot_option ? "boot option: programming\n" : "reset: to the bootloader\n");
    leaving = true;
    stack_port_disarm();
    power_port_down();
    if (program_boot_option && !hw_boot_via_loader()) hw_program_boot_via_loader();
    else hw_reset_to_loader();
}

// Recovery for a blade the controller cannot reach over I2C: the controller
// takes EN low, and once there has also been no controller access for the
// WATCH_S period, the blade resets into its bootloader.
// The reset requires EN low, so it is always initiated by the controller.
// Silence alone never resets the blade: a controller that is restarting,
// updating or absent leaves EN unchanged, and a running port keeps running
// on its last limits. The watch is off until the controller sets it, so a
// blade on the bench is not reset.
static bool watch_controller(uint32_t now) {
    hw_backplane_lock();
    uint32_t n = regmap_transactions();
    hw_backplane_unlock();
    if (n != seen_count) {
        seen_count = n;
        seen_ms = now;
    }
    if (!cfg.watch_s || en || now - seen_ms < (uint32_t)cfg.watch_s * 1000u) return false;
    console_str("EN low, controller silent: ");
    leave_for_loader(false);
    return true;
}

static bool take_controller_input(void) {
    regmap_config_t c;
    hw_backplane_lock();
    bool changed = regmap_config(&c);
    uint8_t cmd = regmap_command();
    hw_backplane_unlock();

    if (changed) {
        cfg = c;
        console_str("config: port ");
        console_str(cfg.port_en ? "on, " : "off, ");
        console_dec(cfg.max_ma);
        console_str(" mA, ");
        console_dec(cfg.max_mv);
        console_str(" mV, watch ");
        console_dec(cfg.watch_s);
        console_str(" s\n");
        if (port_set_limits(cfg.max_ma, cfg.max_mv)) stack_send_capabilities();
    }
    switch (cmd) {
    case BLADE_CMD_SRC_CAP:
        stack_send_capabilities();
        break;
    case BLADE_CMD_HARD_RESET:
        stack_hard_reset();
        break;
    case BLADE_CMD_CLEAR_FAULTS: // the register file has cleared the latch
        if (!line_up) line_raise();
        break;
    case BLADE_CMD_RESET:
        leave_for_loader(false);
        return true;
    case BLADE_CMD_BOOT_OPT:
        leave_for_loader(true);
        return true;
    default:
        break;
    }
    return false;
}

static uint8_t hot_for(uint8_t samples, int16_t t_dc, int16_t limit_dc) {
    bool past = t_dc == SENSE_TEMP_OPEN_DC || t_dc > limit_dc;
    if (!past) return 0;
    return samples < TEMP_TRIP_SAMPLES ? (uint8_t)(samples + 1) : samples;
}

// Follows whether one thermometer is warm. It becomes warm after
// TEMP_TRIP_SAMPLES consecutive readings at or above the warning level, and
// stops being warm as soon as one reading is TEMP_WARN_CLEAR_DC under that
// level. Returns true on the sample that makes it warm, which is when the
// sink is told. A sensor without a reading is a trip, not a warning.
static bool warm_for(bool *warm, uint8_t *samples, int16_t t_dc, int16_t warn_dc) {
    if (t_dc == SENSE_TEMP_OPEN_DC) {
        *warm = false;
        *samples = 0;
        return false;
    }
    if (*warm) {
        if (t_dc < warn_dc - TEMP_WARN_CLEAR_DC) {
            *warm = false;
            *samples = 0;
        }
        return false;
    }
    if (t_dc < warn_dc) {
        *samples = 0;
        return false;
    }
    if (*samples + 1 < TEMP_TRIP_SAMPLES) {
        (*samples)++;
        return false;
    }
    *warm = true;
    return true;
}
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
